Takazudo/zudo-power-usb-pd/doc/src/content/docs/overview/mechanical-design.md

---
title: Mechanical Design
sidebar_position: 5
---

Physical dimensions and mechanical considerations for PCB layout and enclosure design.

Every component on this page lives on **[Board B](./board-b-synth-power.md)** — the
synth power conversion board carries all the tall parts. Board A (USB-PD core) is
all-SMD small-signal apart from its USB-C receptacle and the JST XH interface connector.

## Component Heights

Physical height reference for PCB layout and enclosure design.

### Power Components

| Component | Designator | Package | Height | Notes |
| --- | --- | --- | --- | --- |
| **LM2596S-ADJ** | U2, U3, U4 | TO-263-5 | **4.5mm**  | DC-DC converters |
| **L7812CD2T-TR**  | U6 | TO-263-2 | **4.5mm**  | +12V linear regulator |
| **L7805ABD2T-TR** | U7 | TO-263-2 | **4.5mm**  | +5V linear regulator |
| **CJ7912** | U8 | TO-252-3 (DPAK) | **2.3mm**  | -12V linear regulator |
| **CYA1265-100UH** | L1, L2, L3 | SMD 13.8x12.8mm | **~6-7mm** | Power inductors |
| **63951-1** | J6, J7, J8, J9 | FASTON 250 THT  | **8.89mm** | Power terminals |
| **470uF 35V** | C5, C7, C12, C14, C20-C21, C24-C25 | D10xL10.5mm  | **10.5mm** | Electrolytic (tallest) — decisions (d), neg-rail-cap-bank |
| **470uF 25V** | C3, C11 | D8xL10.5mm | **10.5mm** | Electrolytic (tallest) |
| **100uF 50V** | C9 | D8xL10.2mm | **10.2mm** | Electrolytic, U4 bridging cap |
| **470uF 10V** | C4, C22, C23 | D6.3xL7.7mm | **7.7mm**  | Electrolytic — decision (c) |

<Note title="Where these numbers come from">

Can dimensions follow the [BOM](./bom.md)'s per-part package column, which agrees with the
MPN case codes (`GVT1E477M0810` and `RVT1H101M0810` are Φ8 cans; `RVT1A471M0607` is the
6.3 × 7.7 mm can recorded as `fact-c335982-identity` in the passives bundle). C9's
10.2 mm is separately confirmed in the
[Board B design notes](./board-b-synth-power.md#design-notes-from-the-89-architecture-review).

Both 10.5 mm figures are now **datasheet-verified** (issue #150). The 25 V line's HRK
datasheet states the case three ways on page 1 — the header `GVT, 25v, 470uF, 8x10.5`,
the description `D8H10.5mm`, and a Dimension & Marking table giving A 8.3 / B 8.3 /
C 9.0 / D 8.0 / L 10.5. The 35 V line's FOLLON FVH datasheet lists the 10 × 10.5 case at
A 10.3 / B 10.3 / C 11.2 / L 10.5 ± 0.5, and its own part-number key decodes
`EFVH035ADA471M10B0` as diameter code `10` (Ø10) and height code `B0` (10.5 mm). Recorded
as `fact-c2983319-case-size` in the passives bundle.

</Note>

### Height Profile

```mermaid
xychart-beta
    title "Component Height Profile"
    x-axis ["TO-252 (U8)", "TO-263 (U2-U7)", "Inductors (L1-L3)", "470uF 10V", "FASTON (J6-J9)", "100uF 50V (C9)", "470uF 25/35V"]
    y-axis "Height (mm)" 0 --> 12
    bar [2.3, 4.5, 6.5, 7.7, 8.89, 10.2, 10.5]
```

### PCB Design Implications

- **Tallest components**: 470uF 25V / 35V electrolytic caps (10.5mm)
- **Second tallest**: C9, the 100uF 50V bridging cap (10.2mm)
- **Third tallest**: FASTON terminals J6-J9 (8.89mm)
- **Then**: 470uF 10V electrolytics &amp; inductors (7.7mm / ~6-7mm)
- **Total board height**: ~12mm including PCB thickness (1.6mm)
- **Clearance**: Keep space around TO-263 packages for thermal dissipation
- **CJ7912 advantage**: Lower profile (2.3mm) allows flexible placement
- **FASTON placement**: Position at board edge for cable access
- **Capacitor placement**: Consider grouping tall caps for enclosure fit

## PCB Dimensions

_To be determined based on component placement._

## Heatsink Design

### Aluminum PCB Heatsink Concept

A cost-effective heatsink solution using JLCPCB's aluminum PCB service. The aluminum PCB acts as a custom-fit heatsink that sits on top of the voltage regulators (U6, U7, U8) and DC-DC converters (U2, U3, U4).

#### Design Approach

```
Cross-section view:

    Aluminum PCB (heatsink)
    ┌─────────────────────────────────────────────────────┐
    │░░░░░░░░░░░░░░░░░░░░░░░░░░░░░░░░░░░░░░░░░░░░░░░░░░░░░│
    └──┬──────────┬─────────────────┬─────────────────┬───┘
       │ Thermal  │                 │                 │
       │ Pad      │    (cutout)     │    (cutout)     │
    ┌──┴──┐    ┌──┴──┐           ┌──┴──┐           ┌──┴──┐
    │ IC  │    │ IC  │           │Cap  │           │Cap  │
    │ U6  │    │ U7  │           │     │           │     │
    └─────┘    └─────┘           └─────┘           └─────┘
    ════════════════════════════════════════════════════════
                        Main PCB
```

**Key features:**

1. **Same outline as the Board B PCB** - Easy alignment and mounting
2. **Cutouts for tall components** - Electrolytics (up to 10.5mm), inductors (6-7mm), FASTON terminals
3. **Solid areas over ICs** - TO-263 (4.5mm) and TO-252 (2.3mm) packages for heat transfer
4. **Thermal gap pads** - Fill the gap between IC top surface and aluminum PCB

#### Target Components for Cooling

| Component | Designator | Package  | Height | Heat Dissipation |
| --- | --- | --- | --- | --- |
| L7812CD2T-TR | U6 | TO-263-2 | 4.5mm  | High (1.5V × 1.2A = 1.8W)  |
| L7805ABD2T-TR  | U7 | TO-263-2 | 4.5mm  | High (2.5V × 0.5A = 1.25W) |
| CJ7912 | U8 | TO-252-3 | 2.3mm  | High (1.5V × 0.8A = 1.2W)  |
| LM2596S-ADJ ×3 | U2-U4 | TO-263-5 | 4.5mm  | Medium (switching losses)  |

#### Gap Calculation for Thermal Pads

The gap between IC package top and aluminum PCB bottom depends on:

- Aluminum PCB thickness: ~1.6mm
- Standoff/spacer height: TBD
- IC package height: 2.3mm (TO-252) to 4.5mm (TO-263)

**Recommended thermal pad thickness:** 1mm - 2mm (get multi-thickness pack to test)

### Thermal Gap Pad Selection

Thermal gap pads (サーマルパッド) provide thermal interface between ICs and the aluminum heatsink.

#### Required Specifications

| Spec | Requirement |
| --- | --- |
| Thermal Conductivity | 12+ W/m·K (higher = better) |
| Thickness | 0.5mm - 2mm (measure gap) |
| Size | 100×100mm (cut to fit) |
| Electrical | Non-conductive |
| Material | Silicone-based |

#### Recommended Products

**AliExpress (Budget, 2-4 week shipping):**

| Product | W/m·K  | Size | Price | Link |
| --- | --- | --- | ----- | --- |
| 24W/mK Thermal Pad | **24** | 100×100mm | ~$3 | [AliExpress](https://ja.aliexpress.com/item/1005010519398949.html)  |
| Upsiren 24W/mK | **24** | 100×100mm | ~$3 | [AliExpress](https://www.aliexpress.com/item/1005008513777020.html) |
| Rgeek 12.8W/mK | 12.8 | 100×100mm | ~$5 | [AliExpress](https://www.aliexpress.com/item/1005003167744654.html) |

**Amazon Japan (Fast delivery, 1-2 days):**

| Product | W/m·K | Size | Price | Link |
| --- | ----- | --- | --- | --- |
| OwlTree 3-pack | 12.8  | 100×100mm (0.5/1/1.5mm) | ~¥1,500 | [Amazon.co.jp](https://www.amazon.co.jp/dp/B09DC772PR) |
| Thermalright | 12.8  | 120×120mm | ~¥1,000 | [Amazon.co.jp](https://www.amazon.co.jp/dp/B08ZN832NZ) |
| 17.3W Non-conductive | 17.3  | 100×100mm | ~¥1,500 | [Amazon.co.jp](https://www.amazon.co.jp/dp/B0CM7TF733) |

#### Application Tips

1. **Clean surfaces** - Remove dust and oil from IC and aluminum PCB
2. **Cut to size** - Match IC package footprint (TO-263: ~10×9mm, TO-252: ~6.5×6mm)
3. **Slight compression** - Pads should be 10-20% compressed for optimal contact
4. **No air gaps** - Ensure pad fully covers IC thermal surface

### Ordering Aluminum PCB from JLCPCB

1. **Create edge cuts** in KiCad matching the Board B PCB outline
2. **Add cutouts** for tall components (capacitors, inductors, FASTON terminals)
3. **Export Gerber files** with edge cuts only (no circuit needed)
4. **Order as aluminum PCB** from JLCPCB
5. **Select thickness** based on thermal mass requirements

_Detailed KiCad procedure to be added after prototype testing._

## Enclosure Considerations

_To be added._
