Takazudo/zudo-power-usb-pd/doc/docs/misc/index.mdx

---
sidebar_position: 1
pagination_next: null
pagination_prev: null
---

import CategoryNav from '@site/src/components/CategoryNav';

# Misc

Miscellaneous documentation and reference materials.

This section contains various supplementary documentation that doesn't fit into the main categories.

## Pages in this category

<CategoryNav category="misc" />
