Takazudo/zudo-power-usb-pd/doc/docs/_fragments/ldo-u7-diagram.mdx

import CircuitSvg from '@site/src/components/CircuitSvg';
import LdoU7Svg from '@site/static/circuits/ldo-u7-diagram.svg';

<CircuitSvg src={LdoU7Svg} alt="LM7805 Linear Regulator U7" padding="10px" />

**Capacitor Placement (Critical for PCB layout):**

- **C27/C18 (ceramic)**: Place RIGHT NEXT to IC pins (minimize trace length for high-freq filtering)
- **C22/C23 (electrolytic)**: Can be placed farther from IC (bulk storage, less sensitive to distance)

**Key Points:**

- **Two-stage design**: Buck converter (U3) provides efficient voltage reduction, linear regulator (U7) provides low-noise final output
- **Input capacitor order**: C22 (bulk, farther) and C27 (ceramic, close to IC)
- **Output capacitor order**: C18 (ceramic, close to IC) and C23 (bulk, farther)
- **LED indicator**: Blue LED (LED3) with 330Ω current-limiting resistor shows +5V rail is active
- **LED current**: I = (5V - 2.8V) / 330Ω = 6.67mA (improved brightness vs previous 1kΩ design)
- **Dropout voltage**: LM7805 requires ~2V dropout, so 7.5V input provides 2.5V headroom

**Protection Circuit (+5V Rail, 0.5A target, 1A max):**

- **Protection layers**: LM7805 current limiting (~1A max) → LM7805 thermal shutdown (150°C) → PTC2 trips (&gt;2.2A) → USB-PD adapter protection
- **PTC2**: C70119 (mSMD110-33V) - 1.1A hold, 2.2A trip, auto-reset fuse
- **TVS2**: SD05 (unidirectional, 5V standoff) - Overvoltage protection optimized for DC power rail
- **Operation**: Normal (&lt;1.1A) = PTC low resistance, LED on; Overload (1.1A-2.2A) = PTC heats/trips in 1-5s; Short circuit (&gt;2.2A) = LM7805 current limiting + PTC trips in 1-5s; Auto-reset after 30-60s cooling

<details>
<summary>View ASCII art circuit</summary>

```
Regulator IC:
                    ┌──────────────────┐
+7.5V IN ───────────┤1 IN         OUT 3├──────────── +5V OUT
                    │                  │
                 ┌──┤2 GND             │
                 │  └──────────────────┘
                GND      LM7805
                        (TO-263-2)

Input Capacitors (C27 closest to IC):
+7.5V ───┬────────────────┬─── To IC Pin 1
         │                │
        C22              C27
       470µF            470nF
    electrolytic       ceramic
     (farther)        (CLOSE!)
         │                │
        GND              GND

Output Capacitors (C18 closest to IC):
From IC Pin 3 ──┬────────────────┬─── +5V
                │                │
               C18              C23
              100nF            470µF
             ceramic        electrolytic
             (CLOSE!)        (farther)
                │                │
               GND              GND

Status LED:
+5V ──── R8 (330Ω) ──── LED3 (Blue) ──── GND

Protection Circuit:
+5V OUT ─── PTC2 ───┬─→ To Load
   mSMD110-33V      │
   (1.1A hold)      │
   (2.2A trip)      │
                    │
                   ┌┴┐ TVS2 (SD05)
                   │ │ Unidirectional
                   └┬┘
                    │
                   GND
```

</details>
