Takazudo/zudo-power-usb-pd/doc/docs/_fragments/inverter-u5-diagram.mdx

import CircuitSvg from '@site/src/components/CircuitSvg';
import InverterU5Svg from '@site/static/circuits/inverter-u5-diagram.svg';

<CircuitSvg src={InverterU5Svg} alt="LM2586 Flyback Converter U5" padding="10px" />

**Key Points:**

- **Flyback topology**: LM2586 configured for negative voltage generation from positive input using coupled transformer
- **High current capability**: 3A output capability (easily handles 800mA requirement for -12V rail)
- **Input voltage range**: 4V~40V (safely accepts +15V input)
- **Output voltage**: Adjustable -15V via feedback resistor divider (R7/R8)
- **Switching frequency**: 200kHz (requires appropriate inductor selection)
- **Coupled transformer**: T1 with 1:1 turns ratio (47µH primary, 47µH secondary magnetically coupled)
- **Component count**: Transformer, Schottky diode, feedback network, and compensation network for stable high-current operation

<details>
<summary>View ASCII art circuit</summary>

```
Flyback Converter Configuration (LM2586SX-ADJ):

Input Power and Primary Circuit (Single +15V rail from Diagram1):

+15V IN ────┬───────────────────────────────────────────────┐
            │                                               │
            │                    ┌────────────────┐         │
            ├────────────────────┤7 VIN           │         │
            │                    │                │         │
         ┌──┴──┐                 │  LM2586SX-ADJ  │         │
         │     │                 │   (TO-263-7)   │         │
        C13   C16                │                │         │
       100µF  100nF          ┌───┤4 GND       SW 5├──── T1 Primary (47µH) ─────┘
         │     │             │   │                │
        GND   GND            │   │Freq.Adj./ON/OFF│     (SW internally switches to GND)
                             │   │              1 ├──○  (Float = ON)
                             │   └────────────────┘
                             │
                            GND

Flyback Transformer (T1) - Coupled Windings (2 terminals each side):

   T1 Primary:                       T1 Secondary:
   +15V IN                           GND
      │                                │
      │  ●────────●                    │  ●────────●
      └──┤        ├── SW pin 5         ├──┤        ├─── To D4 Cathode
         │  47µH  │                       │  47µH  │
         │   1    │                       │   2    │
         └────────┘                       └────────┘

   Turns Ratio: 1:1
   (Magnetically coupled on same core - NOT separate inductors)

Secondary Output Rectification (D4):

   From T1 Secondary ──→ D4 Cathode
                            │
                            │ D4 (Schottky)
                            ▼ Anode
                            │
                         -15V OUT

Output Rectification and Filter:

D4 Cathode (from T1 secondary)
   │
   │ D4 (Schottky Diode)
   │ e.g., SS34, MBRS340
   ▼ Anode
   │
   ├────── -15V OUT (To Diagram5: U4 Buck Input)
   │
  C14
 100µF
   │
  GND

Feedback Network (Voltage Divider):

-15V OUT ─── R7 (10kΩ) ───┬─── FB pin 3 (to LM2586)
                          │
                         R8
                       (~920Ω)
                          │
                         GND

Compensation Network (Pin 2):

                    ┌────────────────┐
                    │  LM2586SX-ADJ  │
                    │                │
                    │     COMP pin 2 ├──── R9 (3kΩ) ────┬──── C15 (0.047µF) ──── GND
                    └────────────────┘                  │
                                                       GND

Complete Connection Summary:
- Pin 1 (Freq. Adj. - On/Off): Floating (always enabled)
- Pin 2 (Compensation): Connected to RC compensation network (R9 + C15 to GND)
- Pin 3 (FB): Feedback from voltage divider (R7/R8)
- Pin 4 (GND): Ground reference
- Pin 5 (SW): Switching output → T1 Primary (L4) → +15V IN
- Pin 6 (Freq. Sync.): Not connected
- Pin 7 (VIN): +15V input power

Output voltage: VOUT = -1.23V × (1 + R7/R8) = -15V
For R7=10kΩ: R8 = 920Ω
```

**Component Selection:**

- **T1**: 47µH:47µH coupled flyback transformer (1:1 turns ratio) rated for 3A primary current
- **C13**: 100µF input bulk capacitor (electrolytic, rated for 25V+)
- **C16**: 100nF ceramic decoupling capacitor (X7R, 50V, 0805) - High-frequency filtering
- **C14**: 100µF output capacitor (electrolytic, reversed polarity for negative rail, rated for 25V+)
- **D4**: Schottky diode rated for 3A (e.g., SS34, MBRS340)
- **R7**: 10kΩ feedback resistor (1/4W, 1% tolerance)
- **R8**: ~920Ω feedback resistor (1/4W, 1% tolerance) for -15V output
- **R9**: 3kΩ compensation resistor (1/4W, 1% tolerance)
- **C15**: 0.047µF (47nF) ceramic compensation capacitor (X7R or C0G/NP0)

</details>
