Takazudo/zudo-power-usb-pd/doc/docs/inbox/circuit-diagrams.md

---
sidebar_position: 3
---

import BuckU2Diagram from '../_fragments/buck-u2-diagram.mdx';
import BuckU3Diagram from '../_fragments/buck-u3-diagram.mdx';
import BuckU5Diagram from '../_fragments/buck-u5-diagram.mdx';

# Circuit Diagrams

Complete circuit configuration shown in stages.

## Diagram1: USB-PD Power Supply Section

```
┌───────────────┐                                       ┌────────────────────┐
│ J1 (USB-C)    │                                       │   U1 (CH224Q)      │
│               │                                       │                    │
│ CC1 (A5)      ├───────────────────────────────────────┤7. CC1              │
│               │                                       │                    │
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
