Takazudo/zudo-power-usb-pd/doc/docs/components/index.mdx

---
sidebar_position: 1
pagination_next: null
pagination_prev: null
---

import CategoryNav from '@site/src/components/CategoryNav';

# Components Documentation

Detailed documentation for all electronic components used in the USB-PD modular synthesizer power supply.

## Pages in this category

<CategoryNav category="components" />
