Takazudo/zudo-power-usb-pd/doc/docs/parts/index.md

---
sidebar_position: 1
pagination_next: null
pagination_prev: null
---

# Parts Documentation

This section will contain detailed documentation about components and parts used in the USB-PD modular synthesizer power supply.

## Planned Content

- Component specifications and datasheets
- JLCPCB part numbers and sourcing information
- Footprint requirements and PCB design considerations
- Alternative parts and substitution guidelines
- Stock availability and procurement strategies
- Cost analysis and BOM optimization

---

*Documentation coming soon.*
