Takazudo/zudo-power-usb-pd/doc/src/content/docs/overview/bom.md

---
title: Bill of Materials (BOM)
sidebar_position: 4
---

Complete parts configuration for JLCPCB SMT assembly, across both boards of the
[two-board split](./two-board-plan.md).

Every reference designator, value, and LCSC number on this page is read from the two
`schgen` spec modules — `scripts/schgen/board_a_spec.py` and
`scripts/schgen/board_b_spec.py` — which are the source of truth for
`boards/board-a/board-a.kicad_sch` and `boards/board-b/board-b.kicad_sch`. Part swaps
carry the decision key from `scripts/schgen/decisions.json` that locked them.

<Note title="Stock figures were removed on purpose">

Earlier revisions of this page carried a per-line stock column dated to an unrecorded
pass. Those numbers had gone stale and there is no way to tell from the page when they
were true. **Verify stock and price at order time** — that is the standing instruction in
every wave-6 decision record. Prices below are rough JLCPCB catalog estimates and are
marked where they are an estimate rather than a dated catalog reading.

</Note>

## Stage-to-Board Map

| Stage | Function | Board |
| ----- | --- | ----- |
| **Stage 1** | USB-PD voltage acquisition (STUSB4500 + load switch) | **Board A** |
| **Stage 2** | DC-DC converters | **Board B** |
| **Stage 3** | Linear regulators | **Board B** |
| **Stage 4** | Protection (PTC + TVS) and rail indicators | **Board B** |
| **Stage 5** | Output connectors | **Board B** |

The JST B6B-XH-A interface connector appears on both boards — `J4` on Board A, `J5` on
Board B. See the
[A↔B interface contract](./board-a-usb-pd-core.md#a↔b-interface-contract-locked-—-copied-verbatim-from-90).

## Power Supply Specifications

**Rail budgets** (the currents this design is sized for, per `CLAUDE.md`):

| Rail | Design budget | Regulator | PTC hold / trip |
| ---- | --- | --- | --- |
| **+12V** | 1.2 A | U6 L7812CD2T | 1.5 A / 3.0 A (PTC1) |
| **+5V** | 0.5 A | U7 L7805ABD2T | 1.1 A / 2.2 A (PTC2) |
| **-12V** | 0.8 A | U8 CJ7912 | 1.5 A / 3.0 A (PTC3) |

Total output budget: 12 V × 1.2 A + 5 V × 0.5 A + 12 V × 0.8 A = **26.5 W**.

- **Input**: USB-C PD 15 V, 3 A contract
- **Efficiency**: ~75-80% — a design estimate, not a measurement

<Warning title="1.5 A is a package capability, not a rail budget">

The L78xx family's 1.5 A rating is a property of the package, not of these rails. The
+5 V rail is budgeted at 0.5 A and its L7805ABD2T evidence bundle records `iout-rating`
as 0.5 A; PTC2 holds at 1.1 A, well under 1.5 A. Sizing a load against "1.5 A per rail"
would exceed both the PTC hold currents and the 26.5 W output budget. See
[Board B → PTC2 hold-current rationale](./board-b-synth-power.md#protection-stage-ptc2-hold-current-rationale-on-the-5-v-rail).

</Warning>

<Note title="Performance figures below are design targets, not measurements">

No rail on this design has yet been energized from a negotiated PD contract — all four
JLCPCB orders (v1-v4) failed at USB-PD negotiation. The efficiency and ripple figures on
this page are design intent for the DC-DC + linear topology, and become measurements only
after Board A bring-up. See [Project Status and Plan](../inbox/current-status.md).

</Note>

## Stage 1: USB-PD Voltage Acquisition (Board A)

Source: `scripts/schgen/board_a_spec.py`. The full design rationale for this stage is on
the [Board A: USB-PD Core](./board-a-usb-pd-core.md) page; the table below is the parts
list only.

### Main ICs, connector, and protection

| Symbol | Part Number | Manufacturer Part Number | Description | Package | Price | Application | Reference |
| --- | --- | --- | --- | --- | ----- | --- | --- |
| **U1** | **[C2678061](https://jlcpcb.com/partdetail/C2678061)** | **STUSB4500QTR** | USB-IF certified PD sink | QFN-24 | **$2.50** | PD negotiation (15 V) | [Board A](./board-a-usb-pd-core.md#component-list-lcsc-parts-and-rough-cost) |
| **Q1** | **[C347476](https://jlcpcb.com/partdetail/C347476)** | **AO3401A** (UMW) | P-channel MOSFET -30 V -4 A | SOT-23 | **$0.02** | Load switch (high-side) | [Board A](./board-a-usb-pd-core.md#load-switch-q1-gate-network-and-soft-start) |
| **J1** | **[C456012](https://jlcpcb.com/partdetail/C456012)** | **USB-TYPE-C-009** | 6P Type-C female | SMD | **$0.05** | USB-C input | [Board A](./board-a-usb-pd-core.md#component-list-lcsc-parts-and-rough-cost-j1-substitution-options) |
| **D5** | **[C571370](https://jlcpcb.com/partdetail/C571370)** | **SMAJ20A** | 20 V unidirectional TVS | SMA | **~$0.15** (est.) | VBUS clamp — cathode `VBUS_IN`, anode `GND` | [Board A](./board-a-usb-pd-core.md#deltas-vs-the-current-single-board-circuit) |
| **D8** | **[C92321](https://jlcpcb.com/partdetail/C92321)** | **BZT52C11-7-F** (Diodes Inc.) | Zener, Vz 10.4-11.6 V | SOD-123 | **$0.054** | Q1 gate-source clamp — cathode `VBUS_IN`, anode `Net-(Q1-G)` | [Board A](./board-a-usb-pd-core.md#programming-order-and-the-d8-gate-clamp) |
| **J4** | **[C144397](https://jlcpcb.com/partdetail/C144397)** | **B6B-XH-A(LF)(SN)** (JST) | 6-pin shrouded header, 2.5 mm | THT | **~$0.08** (est.) | Board A → Board B interface | [Board A](./board-a-usb-pd-core.md#a↔b-interface-contract-locked-—-copied-verbatim-from-90) |

<Warning title="D4 (USBLC6-2SC6) is gone, not optional">

Older revisions of this page listed `D4` (USBLC6-2SC6, C7519) under an "ESD Protection
(Recommended)" heading. It was **deleted from the design**, not downgraded: its VBUS-clamp
role was a hard absolute-maximum violation (a 6 V-rated zener on a 15 V rail), and its
CC-ESD role duplicated U1's own integrated 22 V protection while routing CC continuity
through a part-internal flow-through — a silent-failure path that was a live candidate in
the v4 diagnosis. CC1/CC2 now run as direct copper from J1 to U1. See
[Board A → Deltas](./board-a-usb-pd-core.md#deltas-vs-the-current-single-board-circuit).

</Warning>

### Capacitors

| Symbol | Part Number | Specification | Package | Price | Application |
| --- | --- | --- | --- | ----- | --- |
| **C1** | **[C13585](https://jlcpcb.com/partdetail/C13585)** | 10 µF 50 V (CL31A106KBHNNNE) | 1206 | **$0.024** | VBUS bulk filter |
| **C2** | **[C1711](https://jlcpcb.com/partdetail/C1711)** | 100 nF 50 V X7R | 0805 | **$0.0021** | VDD HF decoupling |
| **C30** | **[C15849](https://jlcpcb.com/partdetail/C15849)** | 1 µF 50 V (CL10A105KB8NNNC) | 0603 | **$0.001** | VREG_2V7 decoupling |
| **C34** | **[C15849](https://jlcpcb.com/partdetail/C15849)** | 1 µF 50 V (CL10A105KB8NNNC) | 0603 | **$0.001** | VREG_1V2 decoupling |
| **C35** | **[C1711](https://jlcpcb.com/partdetail/C1711)** | 100 nF 50 V X7R | 0805 | **$0.0021** | Gate soft-start |

### Resistors

| Symbol | Part Number | Value | Description | Package | Price | Application |
| --- | --- | ----- | --- | --- | ----- | --- |
| **R11** | **[C25803](https://jlcpcb.com/partdetail/C25803)** | 100 kΩ | ±1% 100 mW | 0603 | **$0.0005** | Gate pull-up (default OFF) |
| **R12** | **[C23206](https://jlcpcb.com/partdetail/C23206)** | 56 kΩ | ±1% 100 mW | 0603 | **$0.0005** | Gate series resistor from `VBEN` |
| **R13** | **[C23179](https://jlcpcb.com/partdetail/C23179)** | 470 Ω | ±1% 100 mW | 0603 | **$0.0005** | DISCH (U1.9) to `VBUS_OUT` |
| **R14** | **[C23179](https://jlcpcb.com/partdetail/C23179)** | 470 Ω | ±1% 100 mW | 0603 | **$0.0005** | Pin-18 (`VBUS_VS_DISCH`) series R — the v3 fix |
| **R15** | **[C23162](https://jlcpcb.com/partdetail/C23162)** | 4.7 kΩ | ±1% 100 mW | 0603 | **$0.0005** | I2C SCL pull-up (to VREG_2V7) |
| **R16** | **[C23162](https://jlcpcb.com/partdetail/C23162)** | 4.7 kΩ | ±1% 100 mW | 0603 | **$0.0005** | I2C SDA pull-up (to VREG_2V7) |
| **R19** | **[C21189](https://jlcpcb.com/partdetail/C21189)** | 0 Ω | ±1% 100 mW | 0603 | **$0.0005** | CC1DB↔CC1 link (dead-battery termination) |
| **R20** | **[C21189](https://jlcpcb.com/partdetail/C21189)** | 0 Ω | ±1% 100 mW | 0603 | **$0.0005** | CC2DB↔CC2 link (dead-battery termination) |

### DNP provisions (footprint placed, not populated, excluded from BOM/CPL)

| Symbol | Part Number | Value / Part | Package | Why it is DNP |
| --- | --- | --- | --- | --- |
| **R17, R18** | **[C23186](https://jlcpcb.com/partdetail/C23186)** | 5.1 kΩ external Rd | 0603 | Rework insurance only. Fitted, they parallel U1's own always-on internal 5.1 kΩ Rd and put CC termination outside the USB Type-C sink window (2.55 kΩ effective) the moment U1 powers up — the v4 blocker |
| **D6, D7** | **[C85382](https://jlcpcb.com/partdetail/C85382)** | PESD24VS1UB (Nexperia) | SOD-523 | CC-line ESD provision, one per CC line to GND. Fit for enclosed/production builds, not for the bring-up/debug build |

### Zero-cost pads

| Symbol | Form | Purpose |
| --- | ---- | --- |
| **J2** | Pogo pads, 1×4, 2.54 mm (bare copper) | NVM I2C programming — see [NVM Programming Setup](../inbox/nvm-programming.md) |
| **J3** | Pogo pads, 1×8, 2.54 mm (bare copper) | Debug pads |
| **TP1, TP2, TP6** | Test pads, D1.5 mm | `VBUS_OUT` / `GND` / `VBUS_VS_DISCH` probes |

**Stage 1 subtotal: ~$2.90** (fitted parts only, J4 included). U1 alone is ~86% of it.
Matches the itemized figure on
[Board A → Component list](./board-a-usb-pd-core.md#component-list-lcsc-parts-and-rough-cost).

**Key features (STUSB4500 vs the v1.0 CH224D design):**

| Feature | CH224D (v1.0) | STUSB4500 (current) |
| --- | --- | --- |
| **USB-IF certified** | No | **Yes** |
| **Charger compatibility** | ~33% | **~95%+** |
| **Error recovery** | None | **Built-in retry** |
| **Power sequencing** | None | **VBUS_EN_SNK pin** |
| **CC protection** | 8 V | **22 V** |
| **Configuration** | Resistor | **NVM + I2C** |

**Critical notes:**

- **Load switch (Q1)** controls the power path — it only conducts after successful PD negotiation
- **VBUS_EN_SNK** (U1.16, active-low, open-drain) pulls LOW on success, turning Q1 ON
- **Soft-start** via C35 limits inrush: τ = R12 × C35 = 56 kΩ × 100 nF = 5.6 ms
- **NVM programming** is required to configure the 15 V PDO (one-time setup), and must be done **before** first attach to a 20 V-capable source. D8 is the hardware guard for the case where it is not — see [Board A → Programming order and the D8 gate clamp](./board-a-usb-pd-core.md#programming-order-and-the-d8-gate-clamp)

## Stage 2: DC-DC Converters (Board B)

Three LM2596S-ADJ: U2 and U3 as buck converters, U4 in an **inverting buck-boost**
configuration. There is no LM2586 and no SEPIC anywhere in this design — decision (b) in
`scripts/schgen/decisions.json` locks that wording against the schematic.
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
